NicholasAntoniadesEngineer/Signal-Generator/pictures_and_videos/pictures/Installation crew 2.jpg

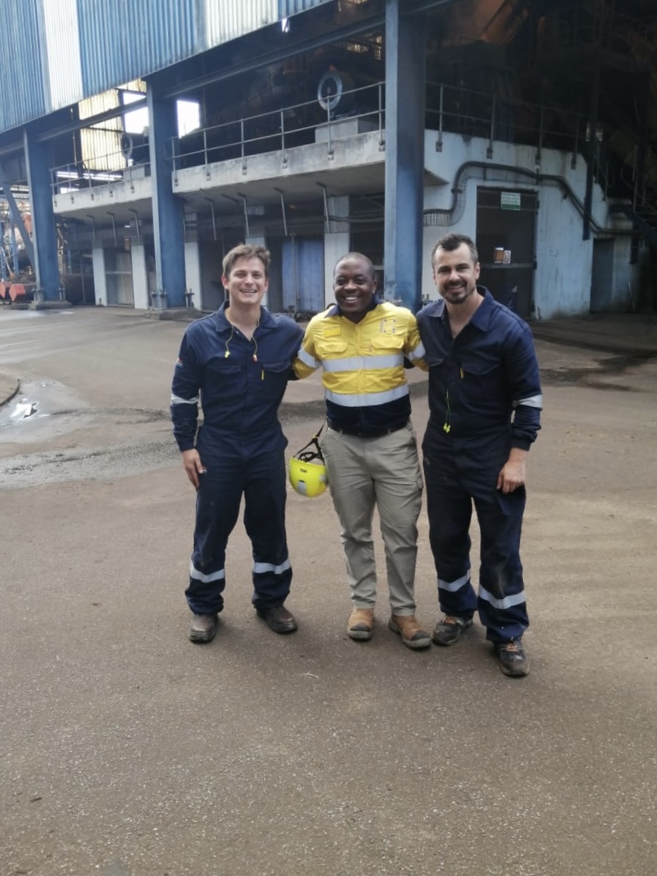
pictures_and_videos/pictures/Installation crew 2.jpg
