NicholasAntoniadesEngineer/Signal-Generator/pictures_and_videos/pictures/System Installation.jpg

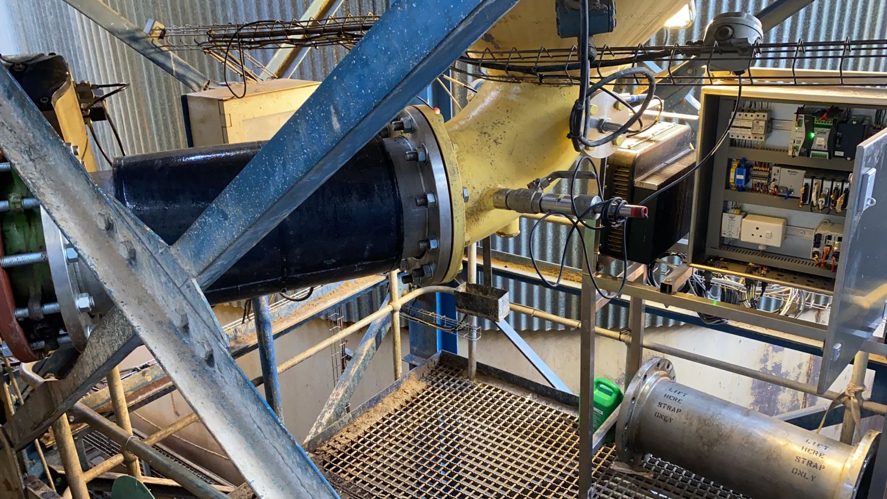
pictures_and_videos/pictures/System Installation.jpg
